UltimateDoge5/Cloudy/driver/logo.h

#include <Arduino.h>

const unsigned char logo[] PROGMEM = {
    0x00, 0x00, 0x00, 0x00, 0x00, 0x00, 0x00, 0x00, 0x00, 0x00, 0x00, 0x00, 0xff, 0xff, 0xfc, 0x00,
    0xff, 0xff, 0xff, 0x00, 0xff, 0xff, 0xff, 0x80, 0xff, 0xff, 0xff, 0xc0, 0xff, 0xff, 0xff, 0xe0,
    0xc0, 0xf3, 0xc7, 0xf0, 0xc0, 0x23, 0xc7, 0xf8, 0xc0, 0x23, 0x8f, 0xfc, 0xc6, 0x03, 0x1f, 0xfe,
    0xc7, 0x02, 0x3f, 0xfe, 0xc7, 0x00, 0x3f, 0xfe, 0xc0, 0x20, 0x3f, 0xfe, 0xc0, 0x20, 0x1f, 0xfe,
    0xc0, 0xe1, 0x1f, 0xfe, 0xc7, 0xe3, 0x8f, 0xfe, 0xc7, 0xe3, 0x87, 0xfe, 0xc7, 0xe3, 0xc3, 0xfe,
    0x07, 0xe3, 0xc1, 0xfe, 0x7f, 0xff, 0xff, 0xfe, 0x1f, 0xff, 0xff, 0xfe, 0x0f, 0xff, 0xff, 0xfe,
    0x07, 0xff, 0xff, 0xfe, 0x03, 0xff, 0xff, 0xfe, 0x01, 0xff, 0xff, 0xfe, 0x00, 0xff, 0xff, 0xfe,
    0x00, 0x7f, 0xff, 0xfe, 0x00, 0x00, 0x00, 0x00, 0x00, 0x00, 0x00, 0x00, 0x00, 0x00, 0x00, 0x00};
